tkircher/Coffee_machine_controller/3D models/01x06_header.step

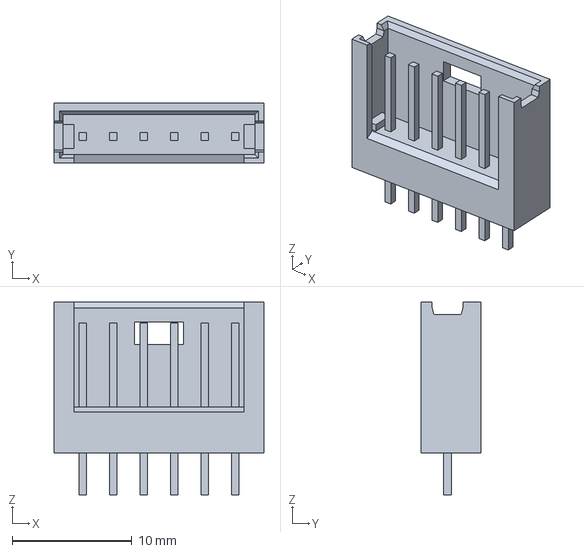
[picture p17: CAD file, 2025-01-06]
3D models/01x06_header.step
17.5 x 5.00 x 16.1 mm
