tkircher/Coffee_machine_controller/3D models/01x04_header.step

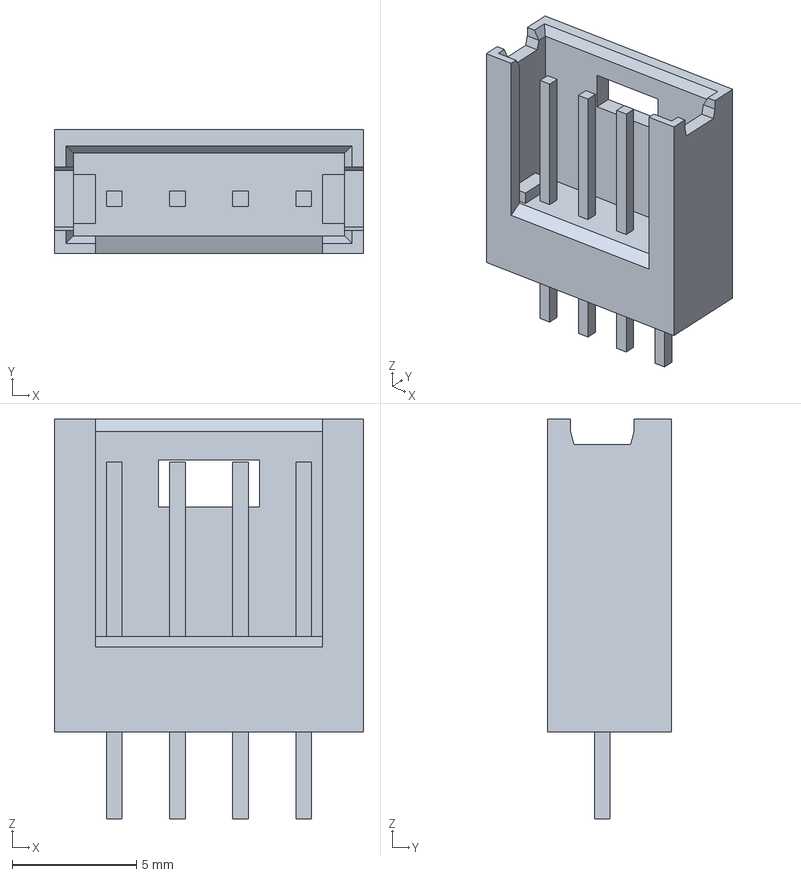
[picture p18: CAD file, 2025-01-06]
3D models/01x04_header.step
12.4 x 5.00 x 16.1 mm
