tkircher/Coffee_machine_controller/3D models/aq1208.step

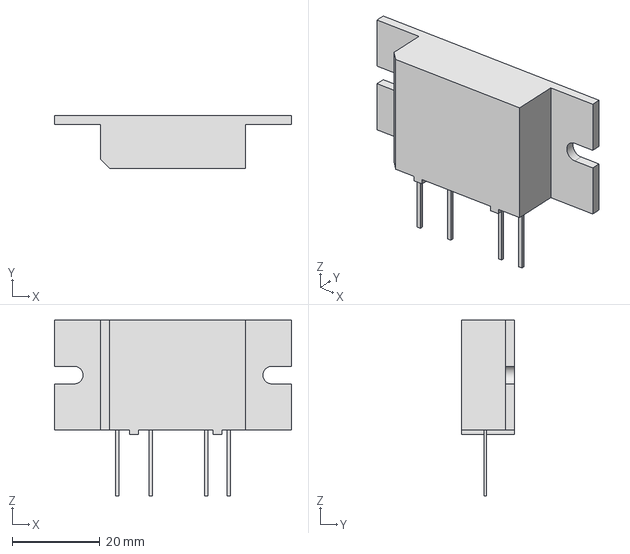
[picture p19: CAD file, 2025-01-06]
3D models/aq1208.step
54.0 x 12.0 x 40.0 mm
