tkircher/Coffee_machine_controller/3D models/RAC05-05SK.step

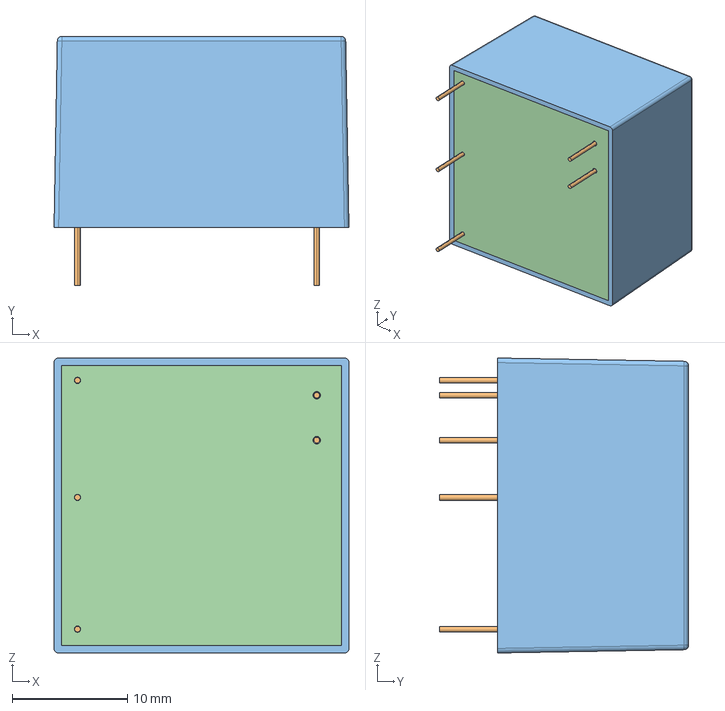
[picture p20: CAD file, 2025-01-06]
3D models/RAC05-05SK.step
25.6 x 21.6 x 25.6 mm
