tkircher/Coffee_machine_controller/3D models/01x02_socket.step

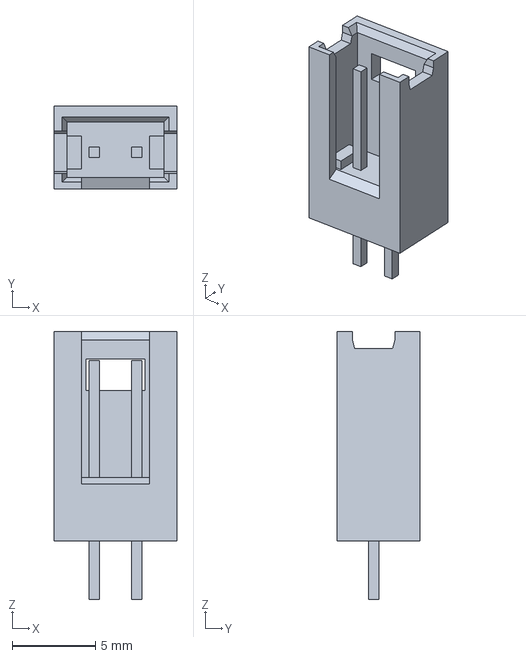
[picture p21: CAD file, 2025-01-06]
3D models/01x02_socket.step
7.37 x 5.00 x 16.1 mm
